GRIDAEI/pipboy-esp32/FABRYKA-IMG-DO-ESP32/Klan Nr 15 (2000)_0001.png

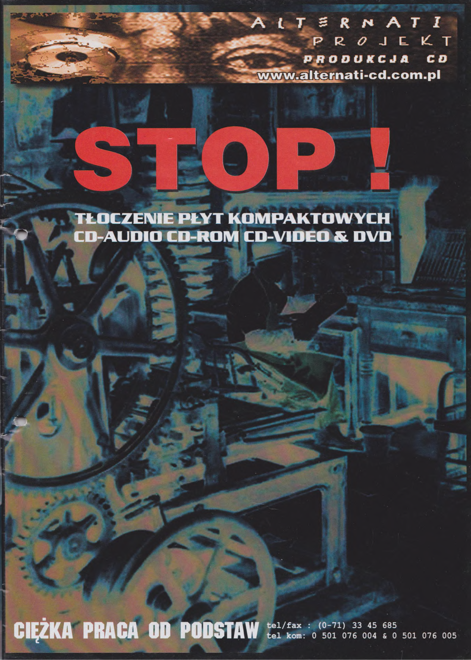
FABRYKA-IMG-DO-ESP32/Klan Nr 15 (2000)_0001.png
