GRIDAEI/pipboy-esp32/FABRYKA-IMG-DO-ESP32/PrimmReputation.webp

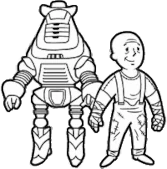
FABRYKA-IMG-DO-ESP32/PrimmReputation.webp
