GRIDAEI/pipboy-esp32/FABRYKA-IMG-DO-ESP32/WorldMapSprite.png

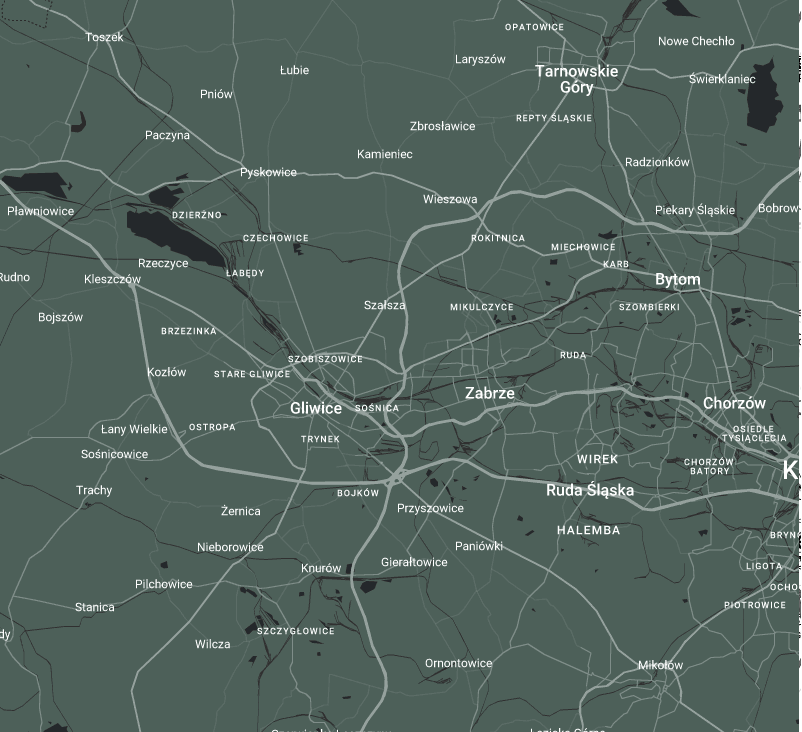
FABRYKA-IMG-DO-ESP32/WorldMapSprite.png
